CocoaFudge/MiniFighter/PICS/Screenshot 2022-06-12 031933.png

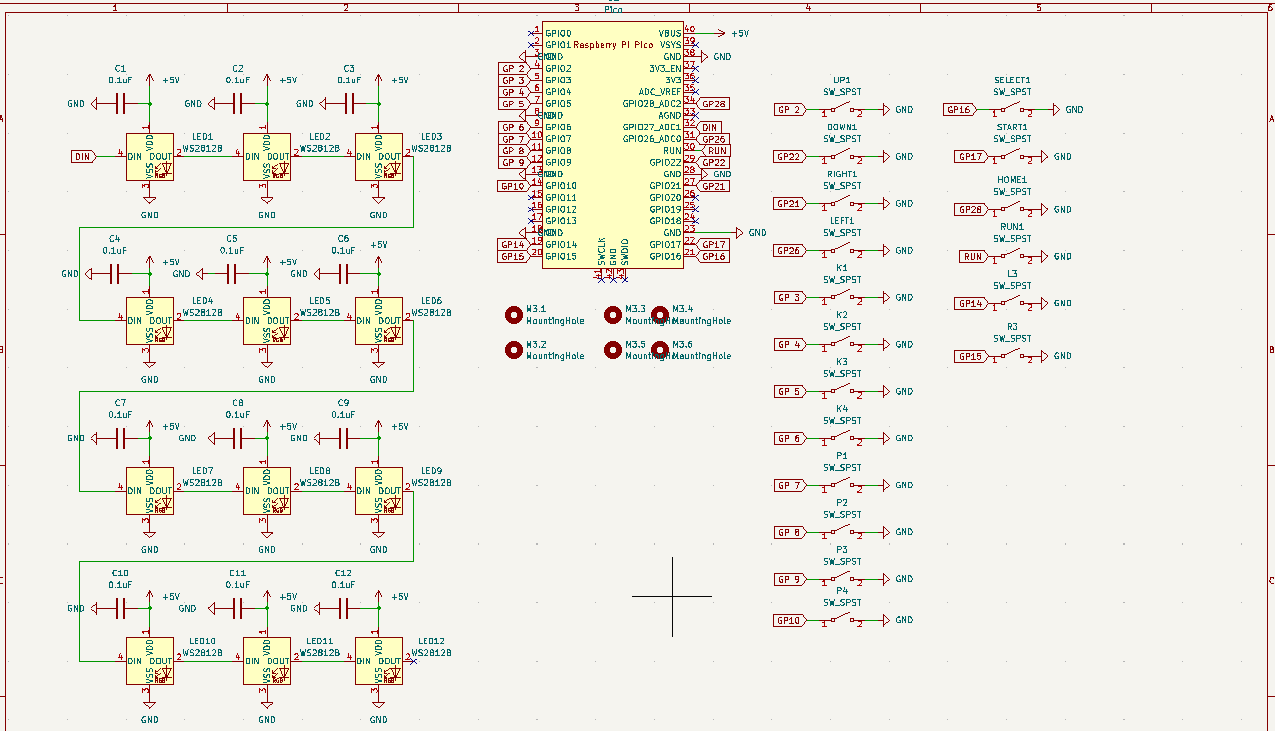
PICS/Screenshot 2022-06-12 031933.png
